VTBajaTesting/testing-suite/StrainGaugeInfo/Draft1_StrainGauge.asc

R1: res
R2: res
R3: res
R4: res
V1: voltage; 5
V2: voltage; 5
Named nets: 0, OUT
